paenian/Rostock-Redux/motor_mount.stl

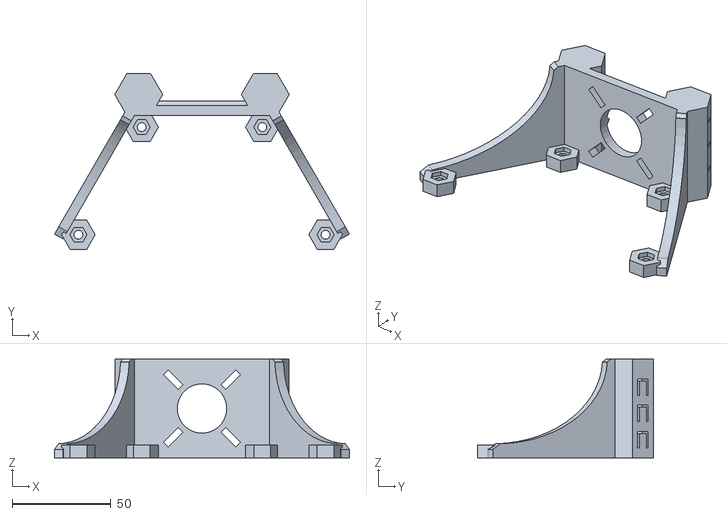
[picture p15: CAD file, 2012-10-15]
motor_mount.stl
149.2 x 88.8 x 50.0
