paenian/Rostock-Redux/SynchromeshIdler.stl

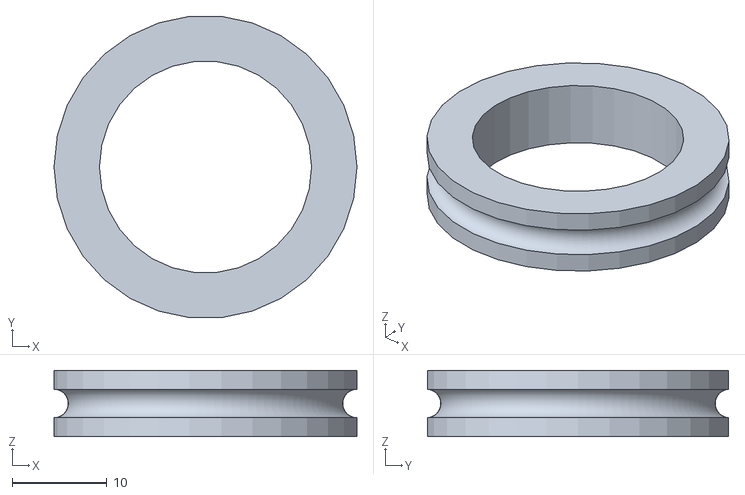
[picture p16: CAD file, 2012-10-15]
SynchromeshIdler.stl
32.0 x 31.8 x 7.00
