paenian/Rostock-Redux/idler_mount.stl

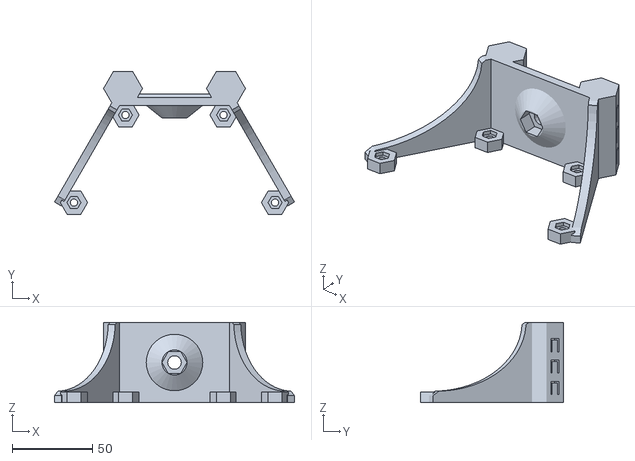
[picture p17: CAD file, 2012-10-15]
idler_mount.stl
149.2 x 88.8 x 50.0
