paenian/Rostock-Redux/joint.stl

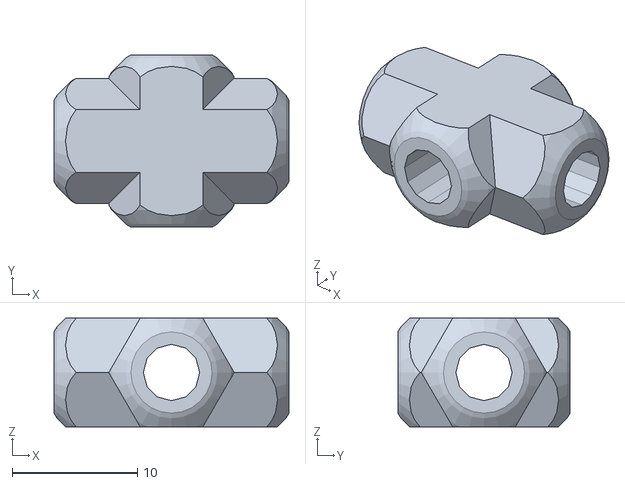
[picture p18: CAD file, 2012-10-15]
joint.stl
18.7 x 13.7 x 8.66
